stuartpittaway/diyBMSv4/ControllerCircuit/DIN_Rail_Case_Dimensions.jpeg

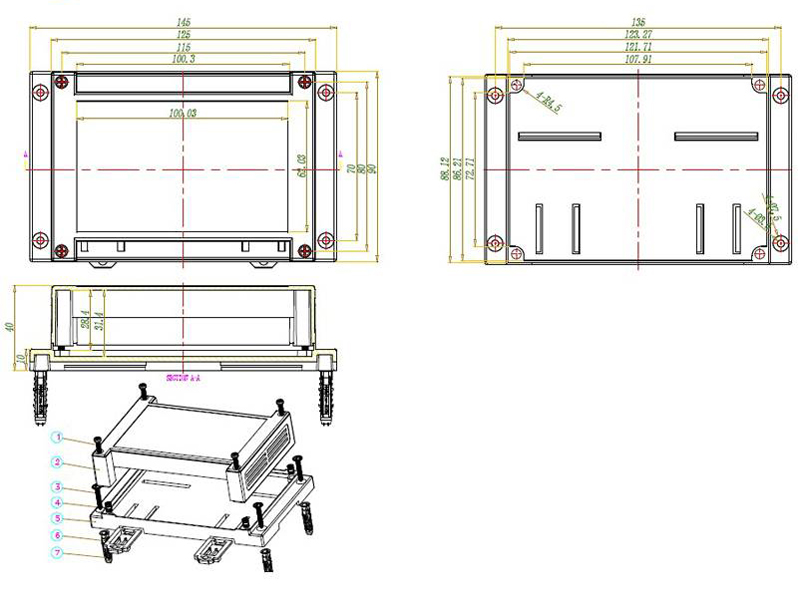
ControllerCircuit/DIN_Rail_Case_Dimensions.jpeg
