stuartpittaway/diyBMSv4/ControllerCircuit/ESP32boards.png

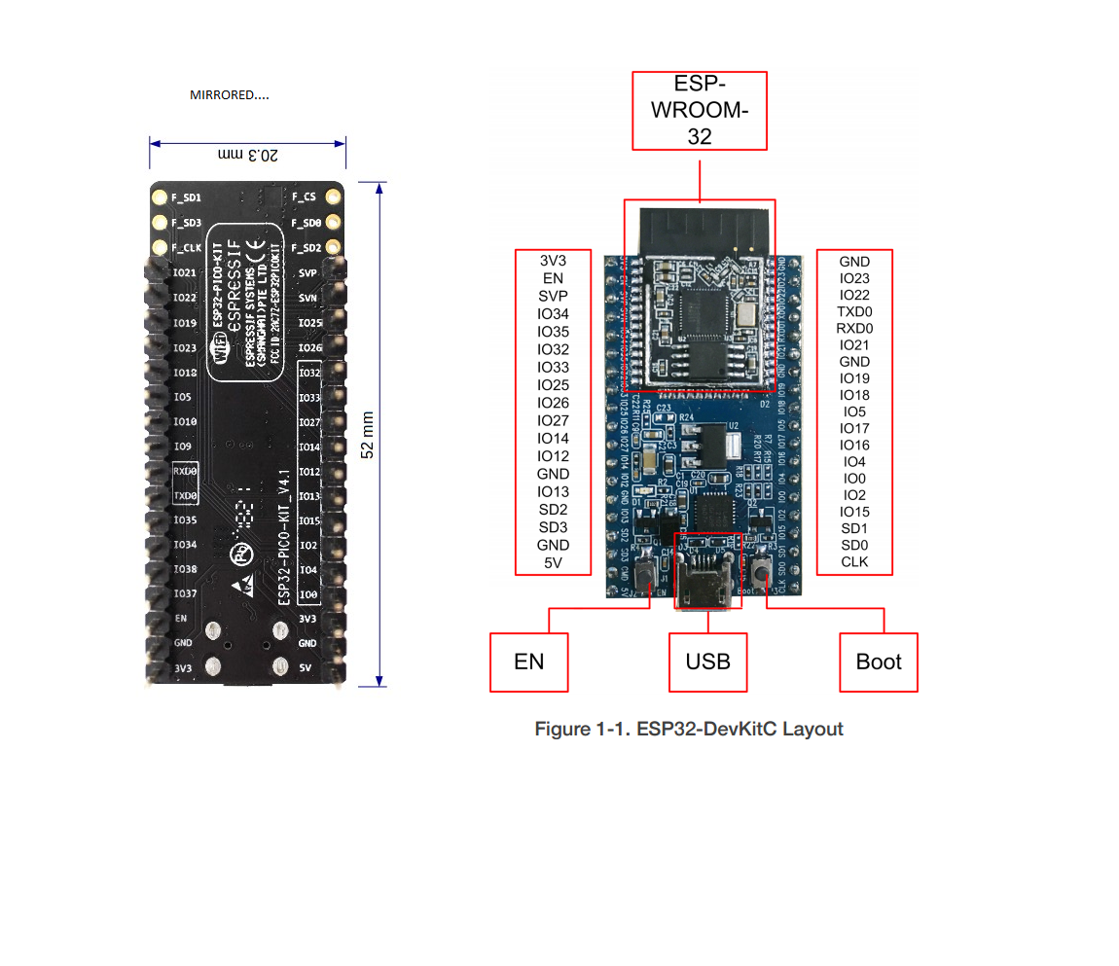
ControllerCircuit/ESP32boards.png
