stuartpittaway/diyBMSv4/ControllerCurrentShuntAddOn/export/ControllerCurrentShuntAddOn-bottom.png

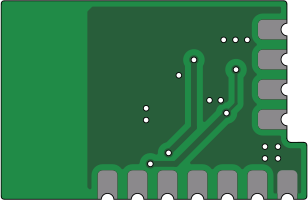
ControllerCurrentShuntAddOn/export/ControllerCurrentShuntAddOn-bottom.png
