stuartpittaway/diyBMSv4/ControllerCurrentShuntAddOn/export/ControllerCurrentShuntAddOn-top.png

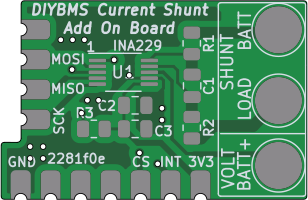
ControllerCurrentShuntAddOn/export/ControllerCurrentShuntAddOn-top.png
