stuartpittaway/diyBMSv4/ModuleV450/export/ModuleV450-bottom.png

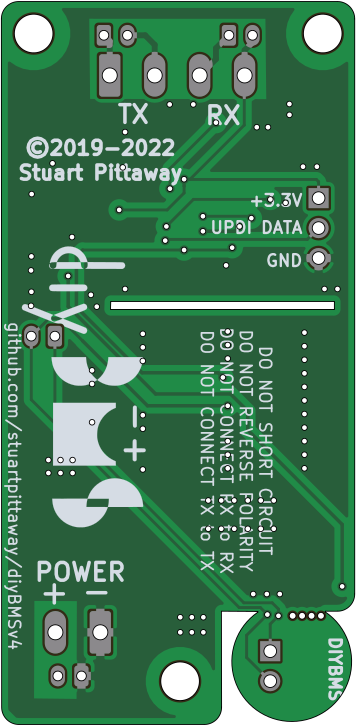
ModuleV450/export/ModuleV450-bottom.png
