stuartpittaway/diyBMSv4/ModuleV490-AllInOne/export/Module_16S-bottom.png

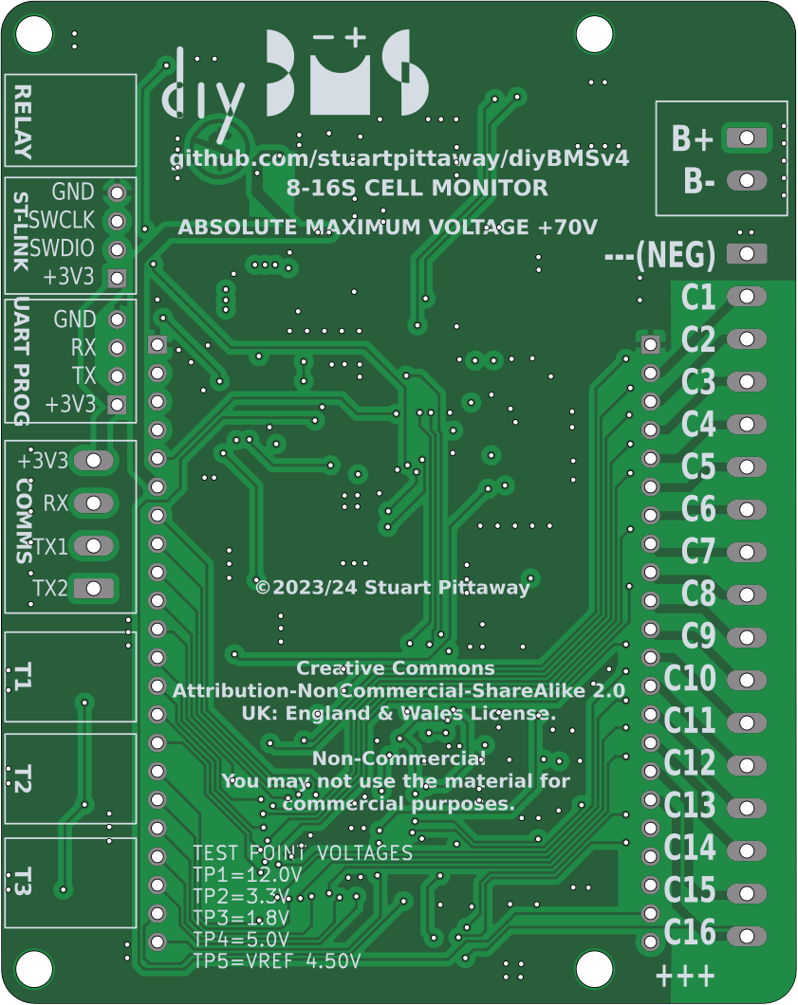
ModuleV490-AllInOne/export/Module_16S-bottom.png
