stuartpittaway/diyBMSv4/ModuleV490-AllInOne/export/Module_16S-top.png

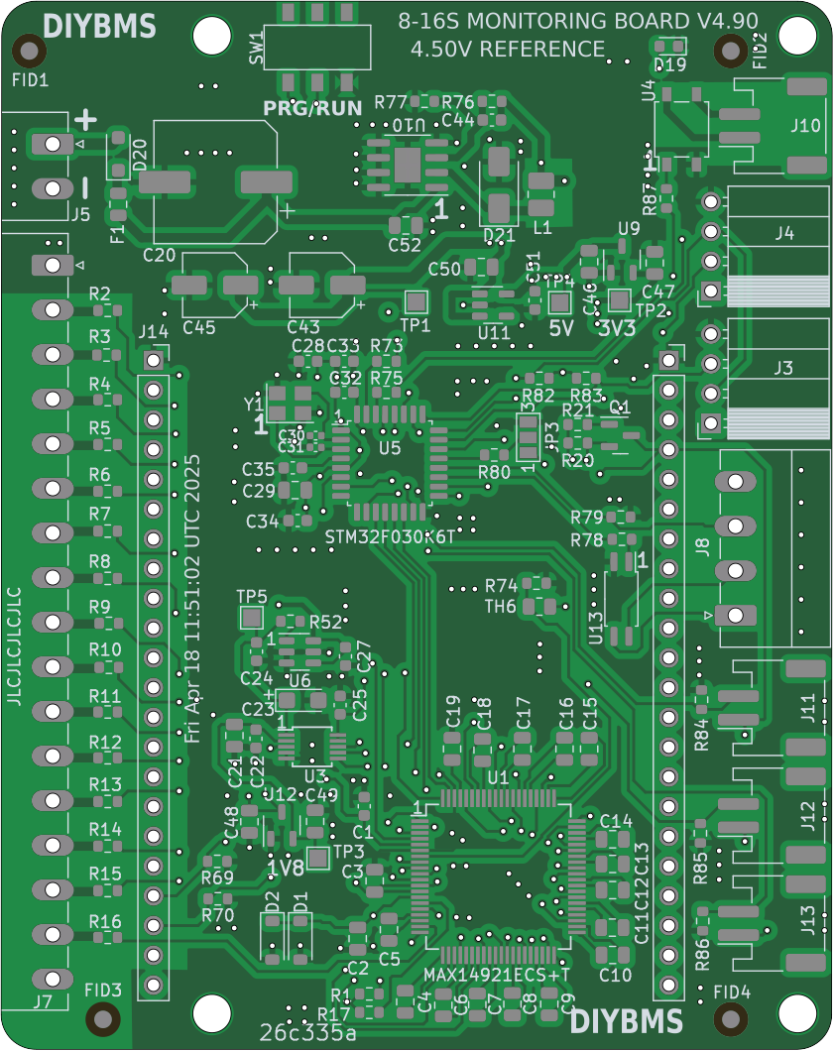
ModuleV490-AllInOne/export/Module_16S-top.png
