stuartpittaway/diyBMSv4/ModuleV490-PassiveBal/export/Module_16S_PassiveBalanceAddOn-bottom.png

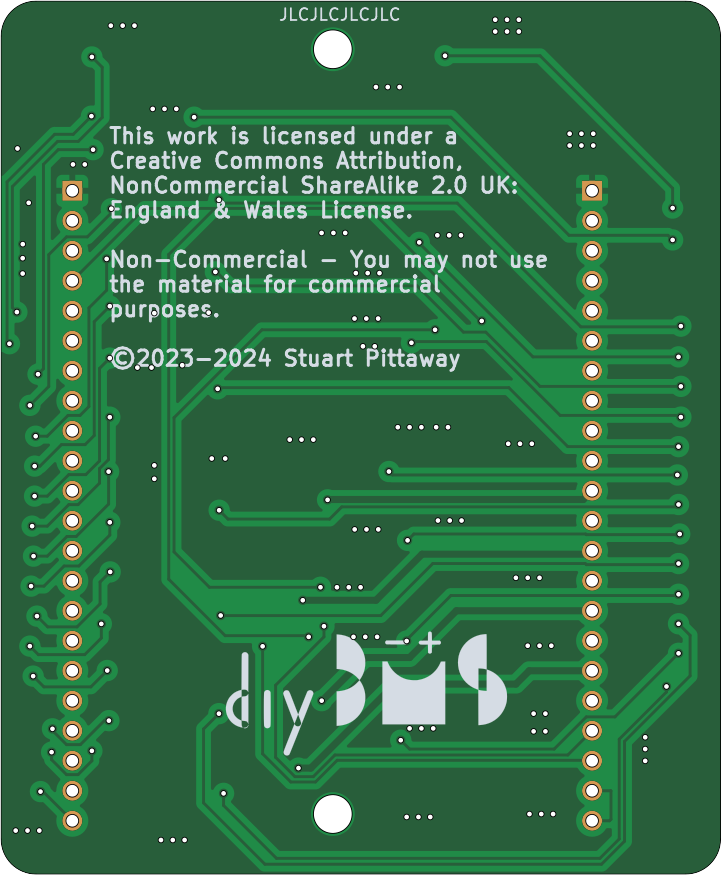
ModuleV490-PassiveBal/export/Module_16S_PassiveBalanceAddOn-bottom.png
