stuartpittaway/diyBMSv4/TemperaturePCB/export/TemperaturePCB-bottom.png

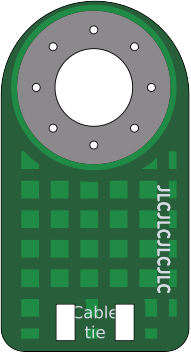
TemperaturePCB/export/TemperaturePCB-bottom.png
