stuartpittaway/diyBMSv4/ModuleV490-AllInOne/export/PCB.pdf

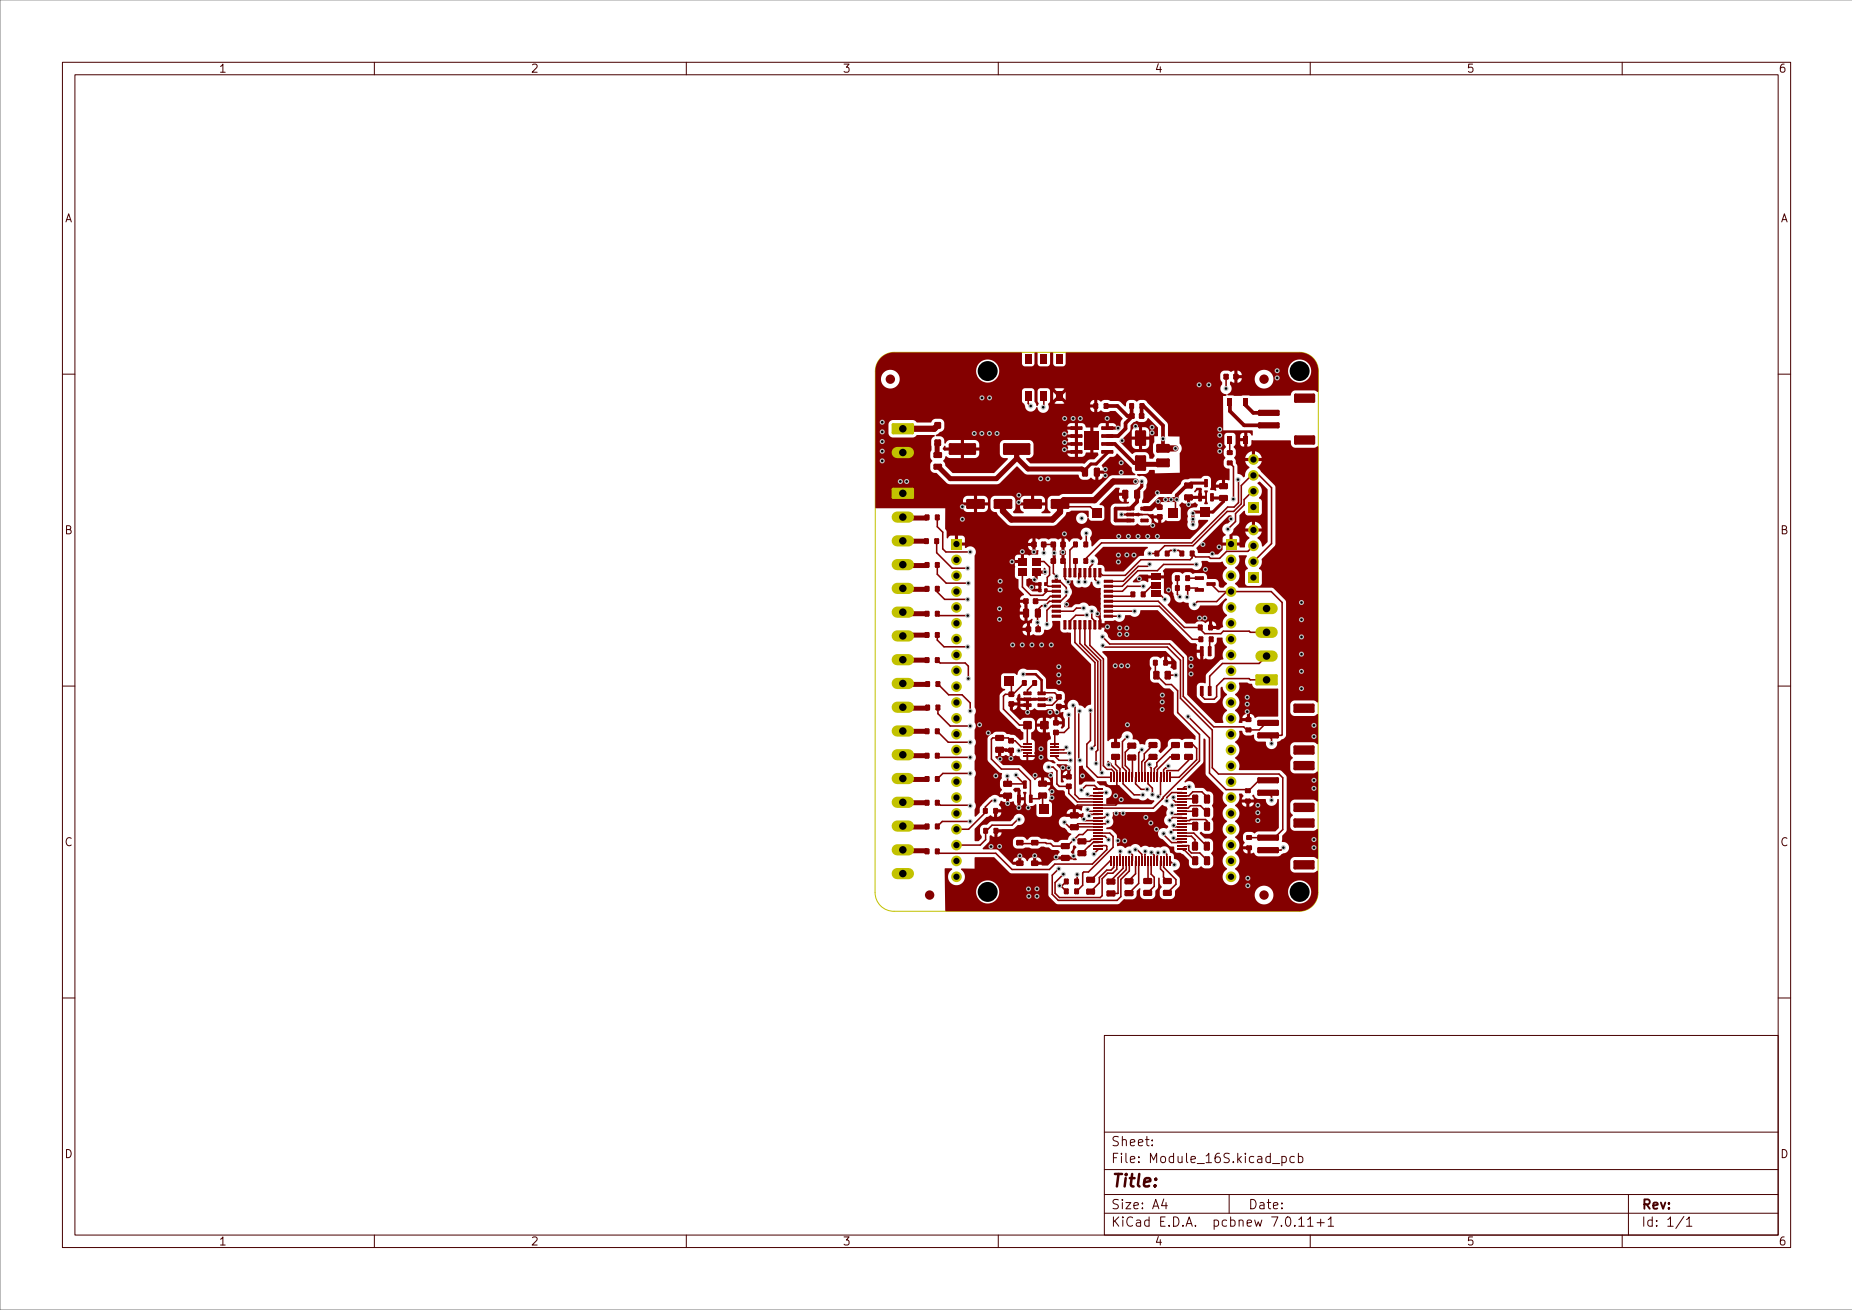
[picture p57: page 1]

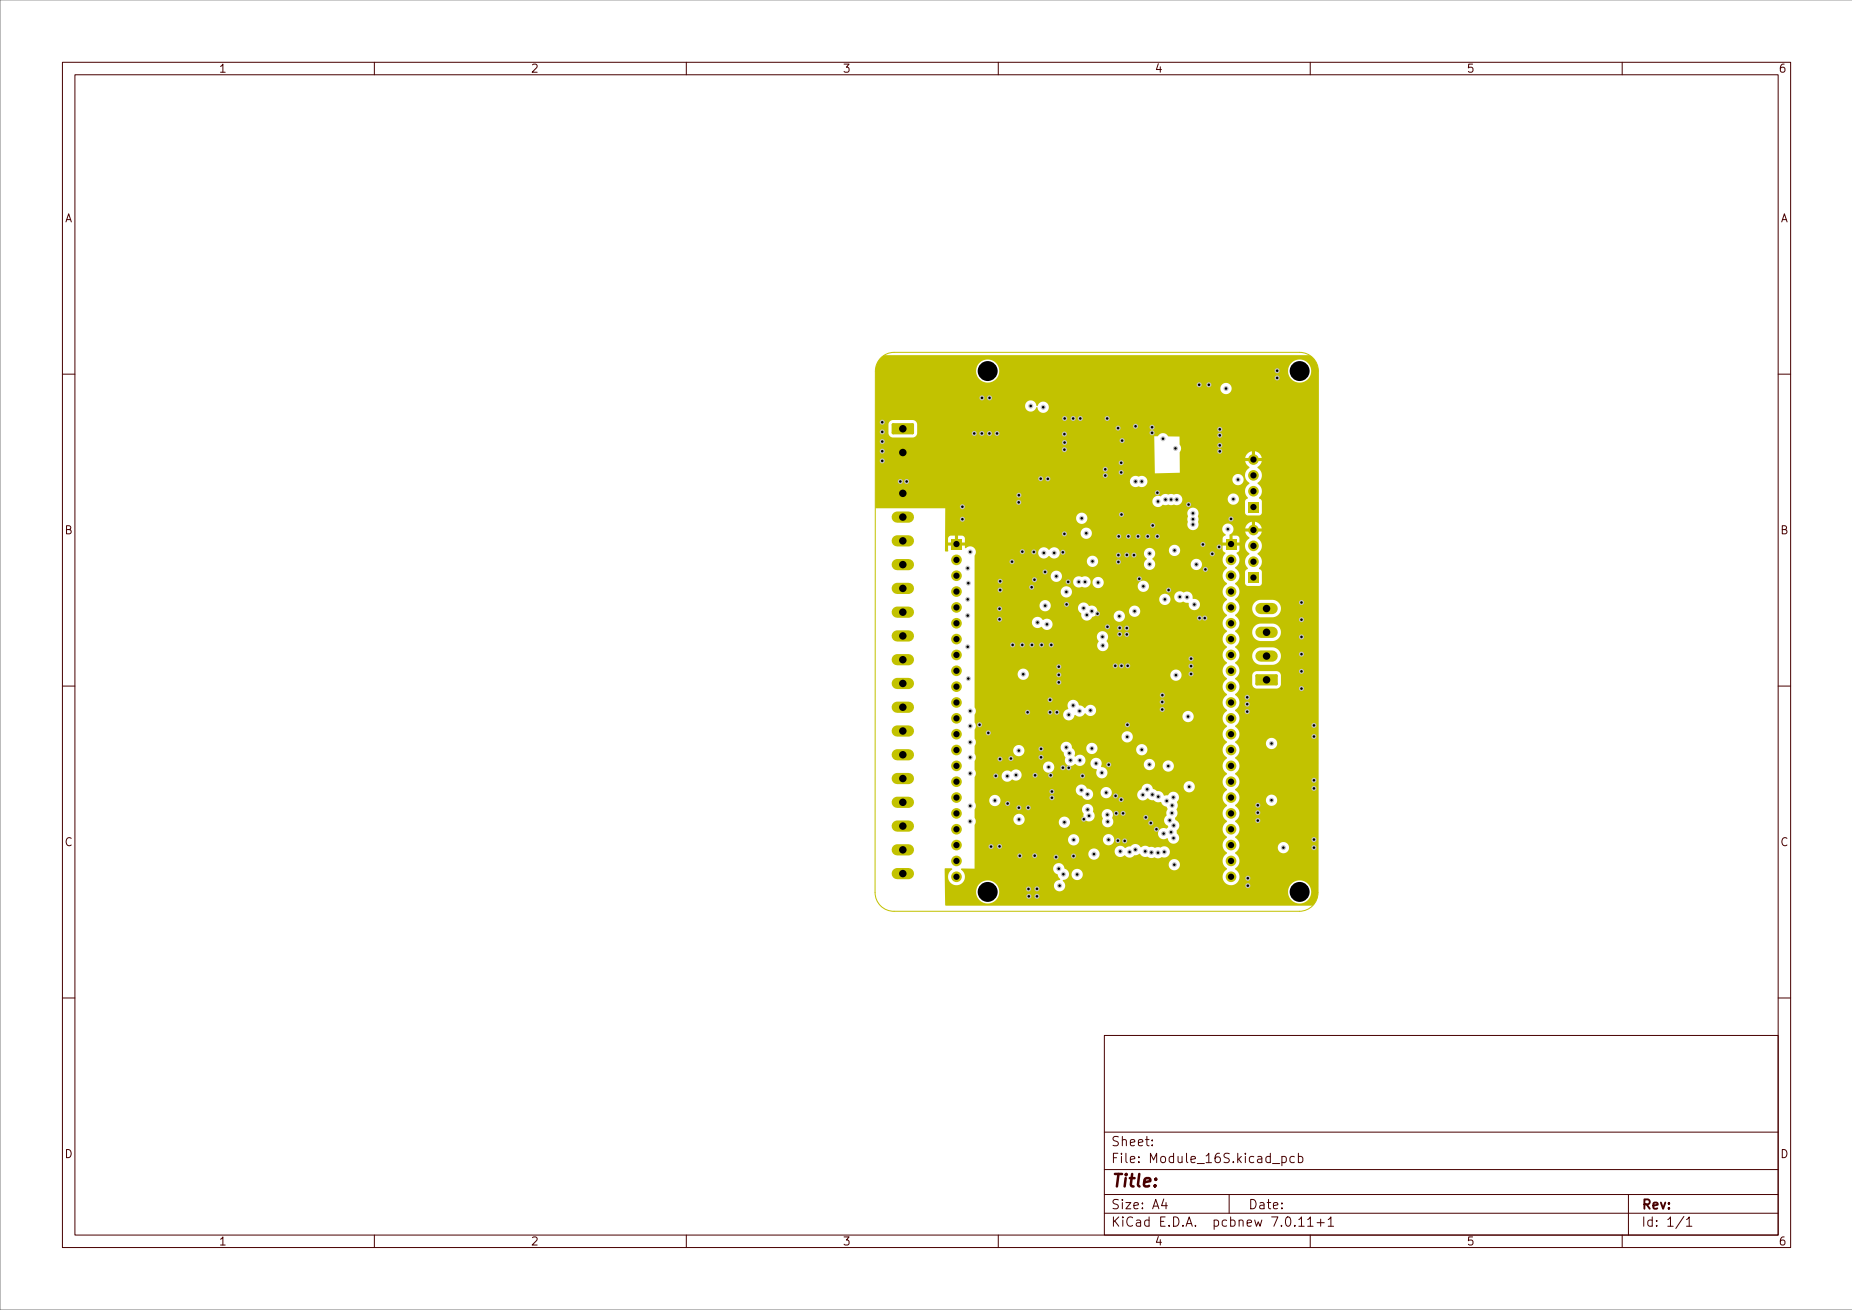
[picture p58: page 2]

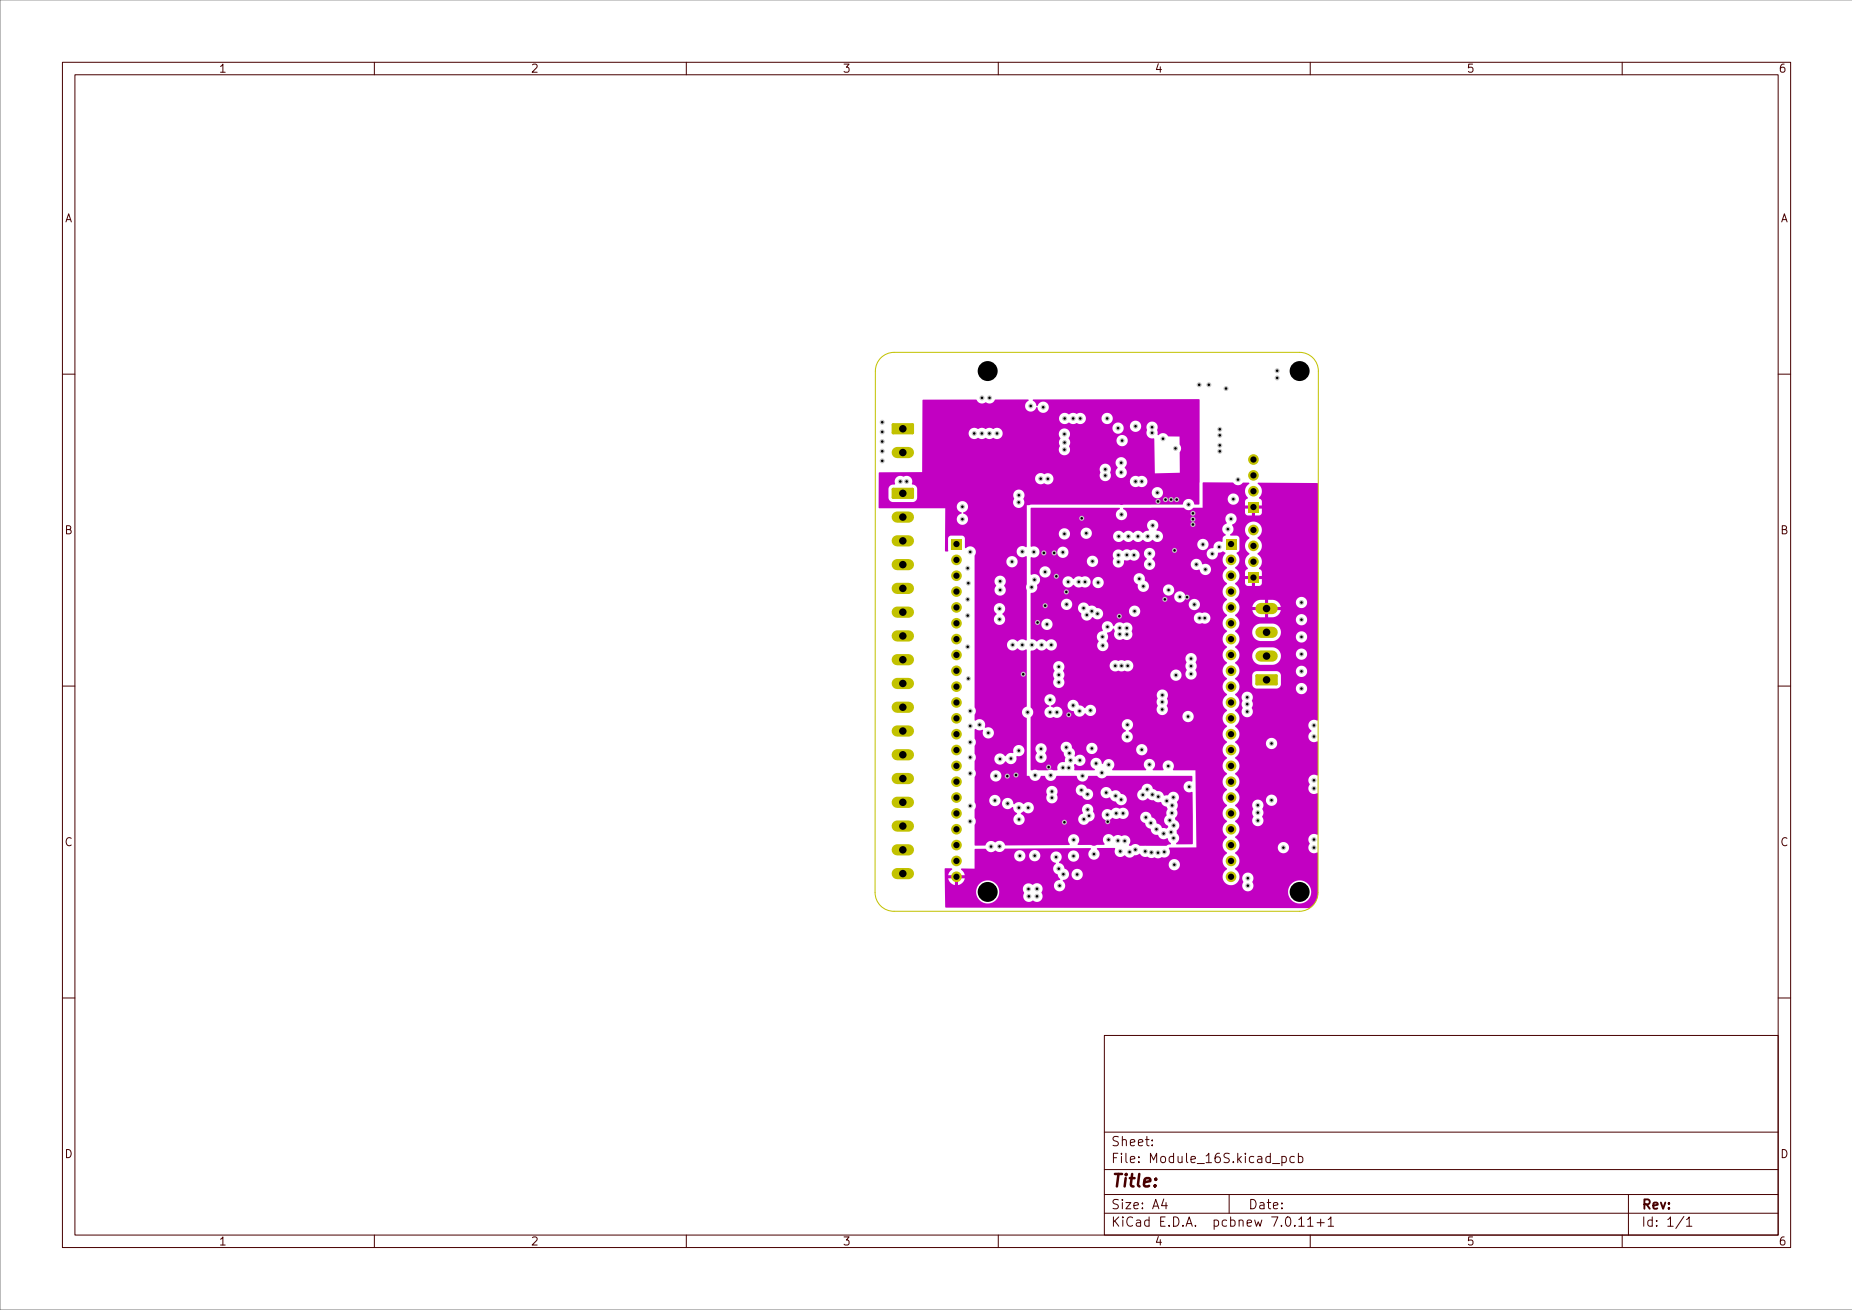
[picture p59: page 3]

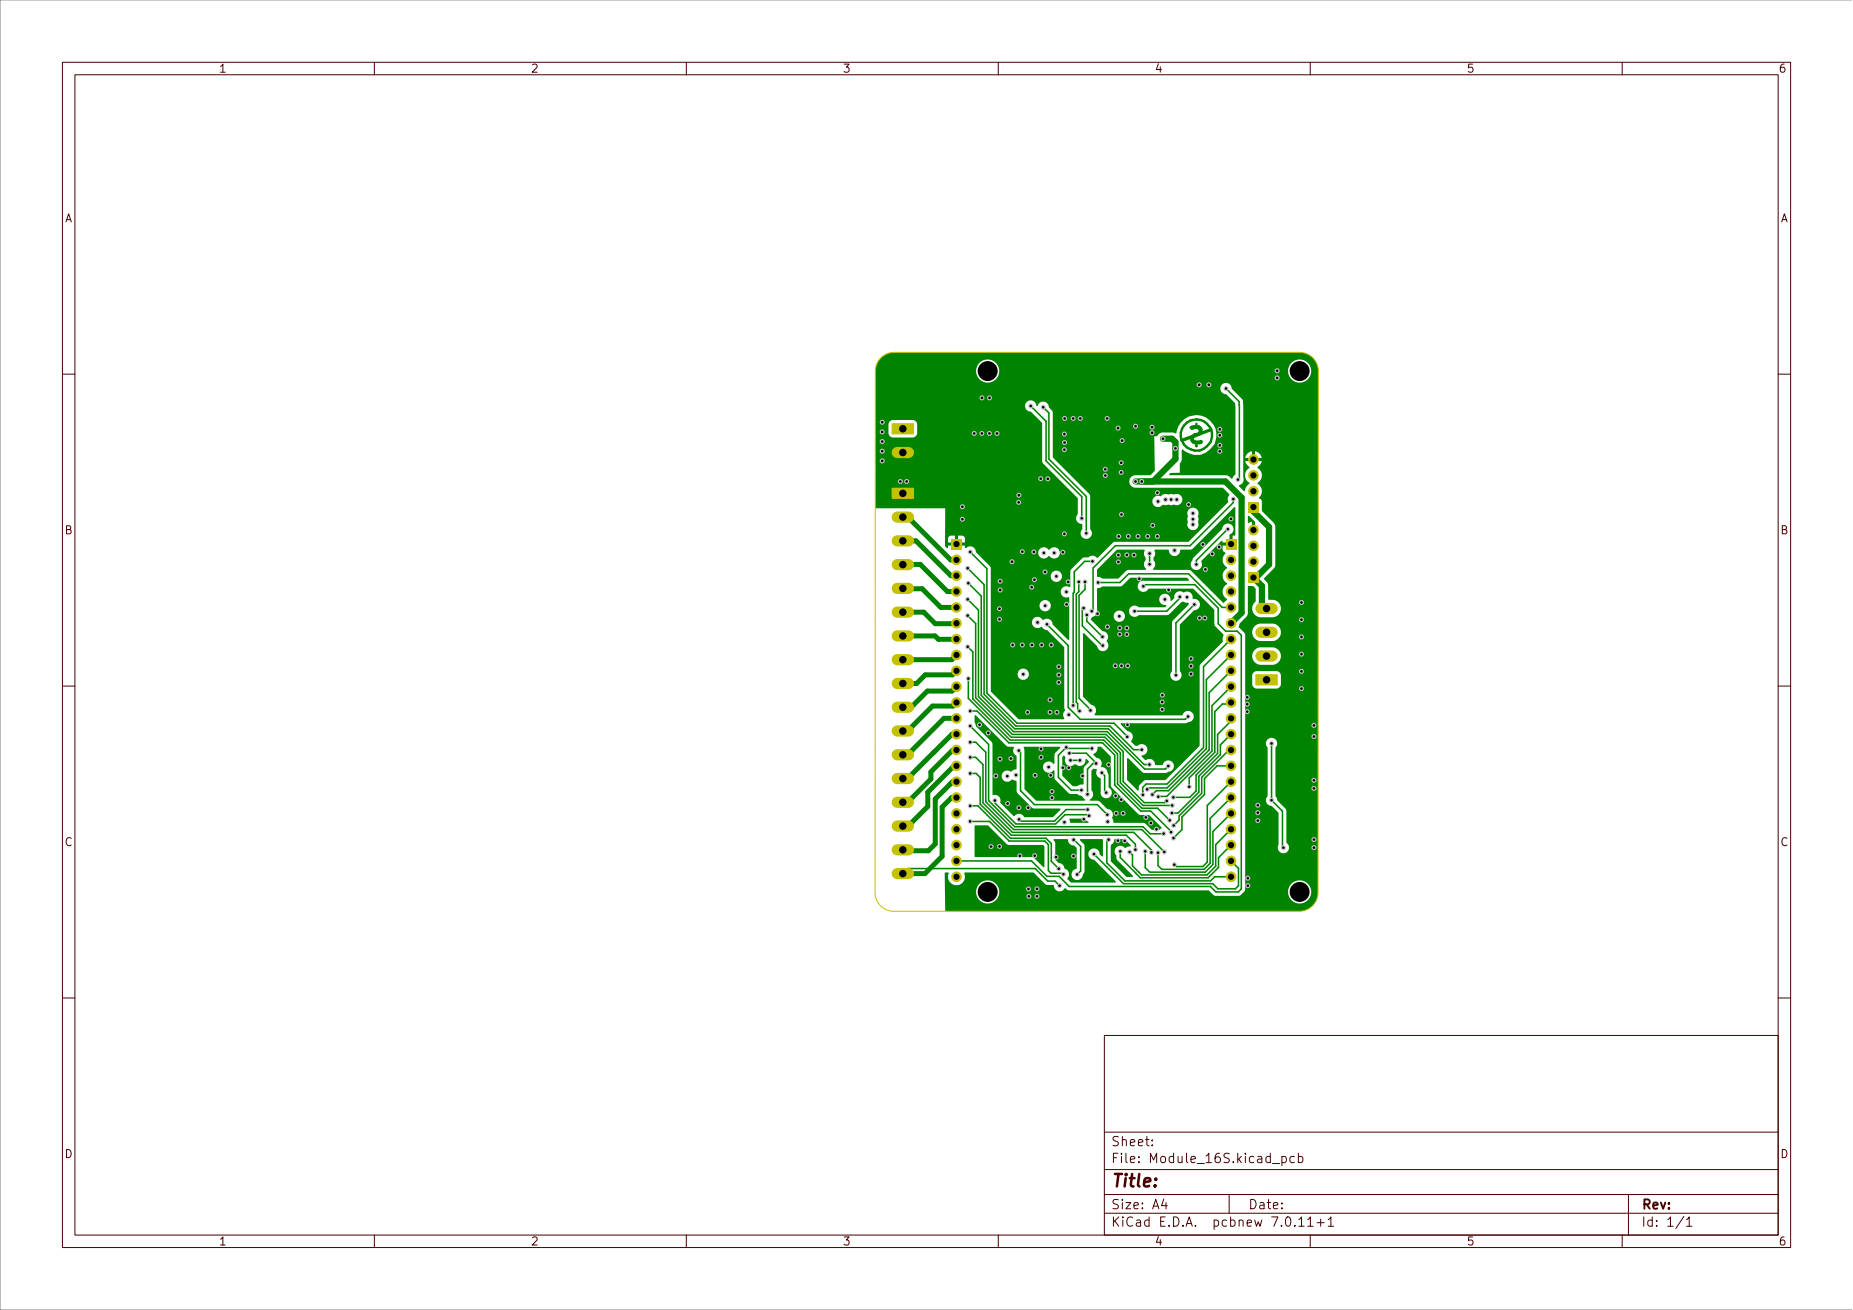
[picture p60: page 4]

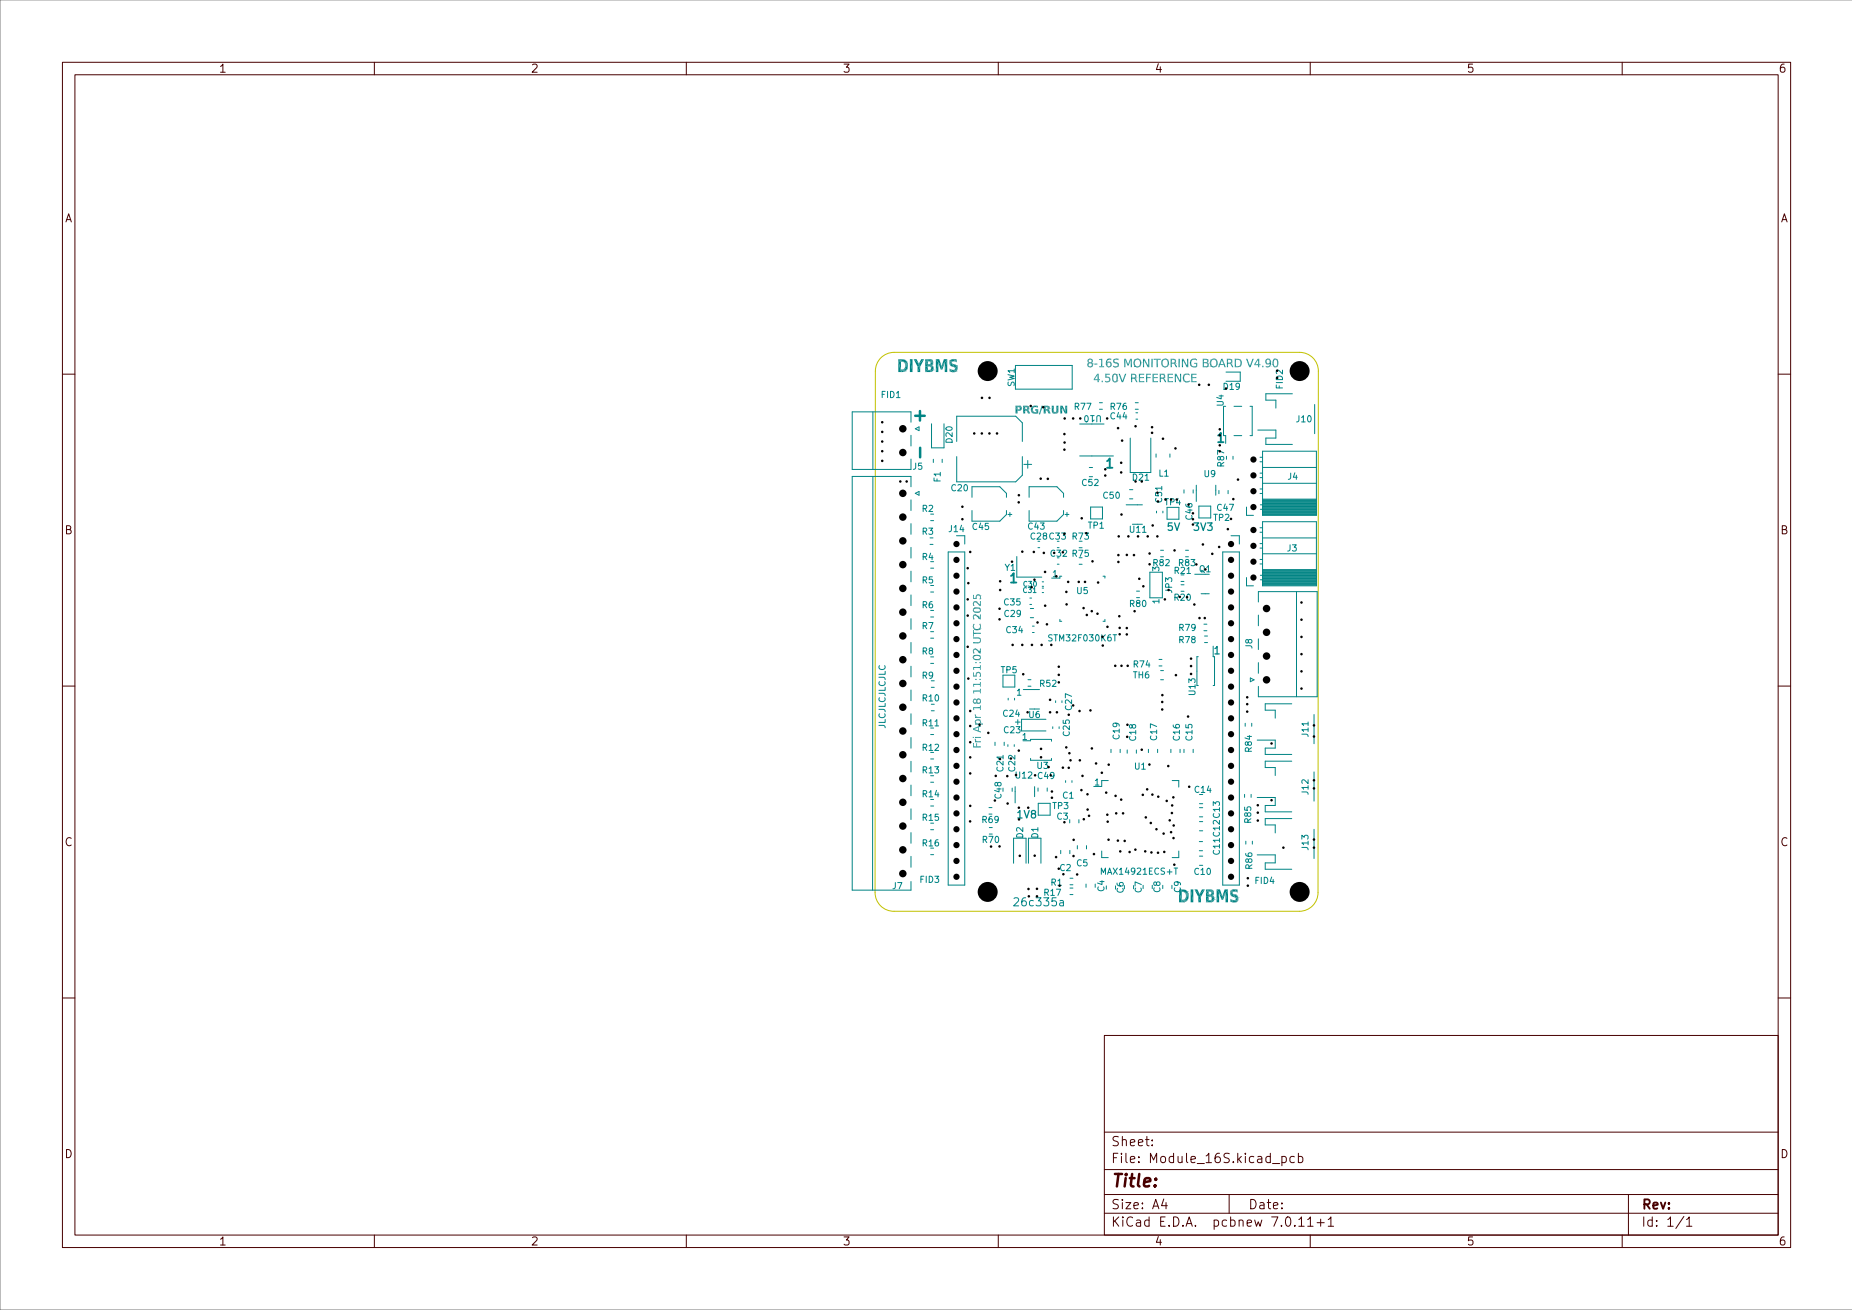
[picture p61: page 5]

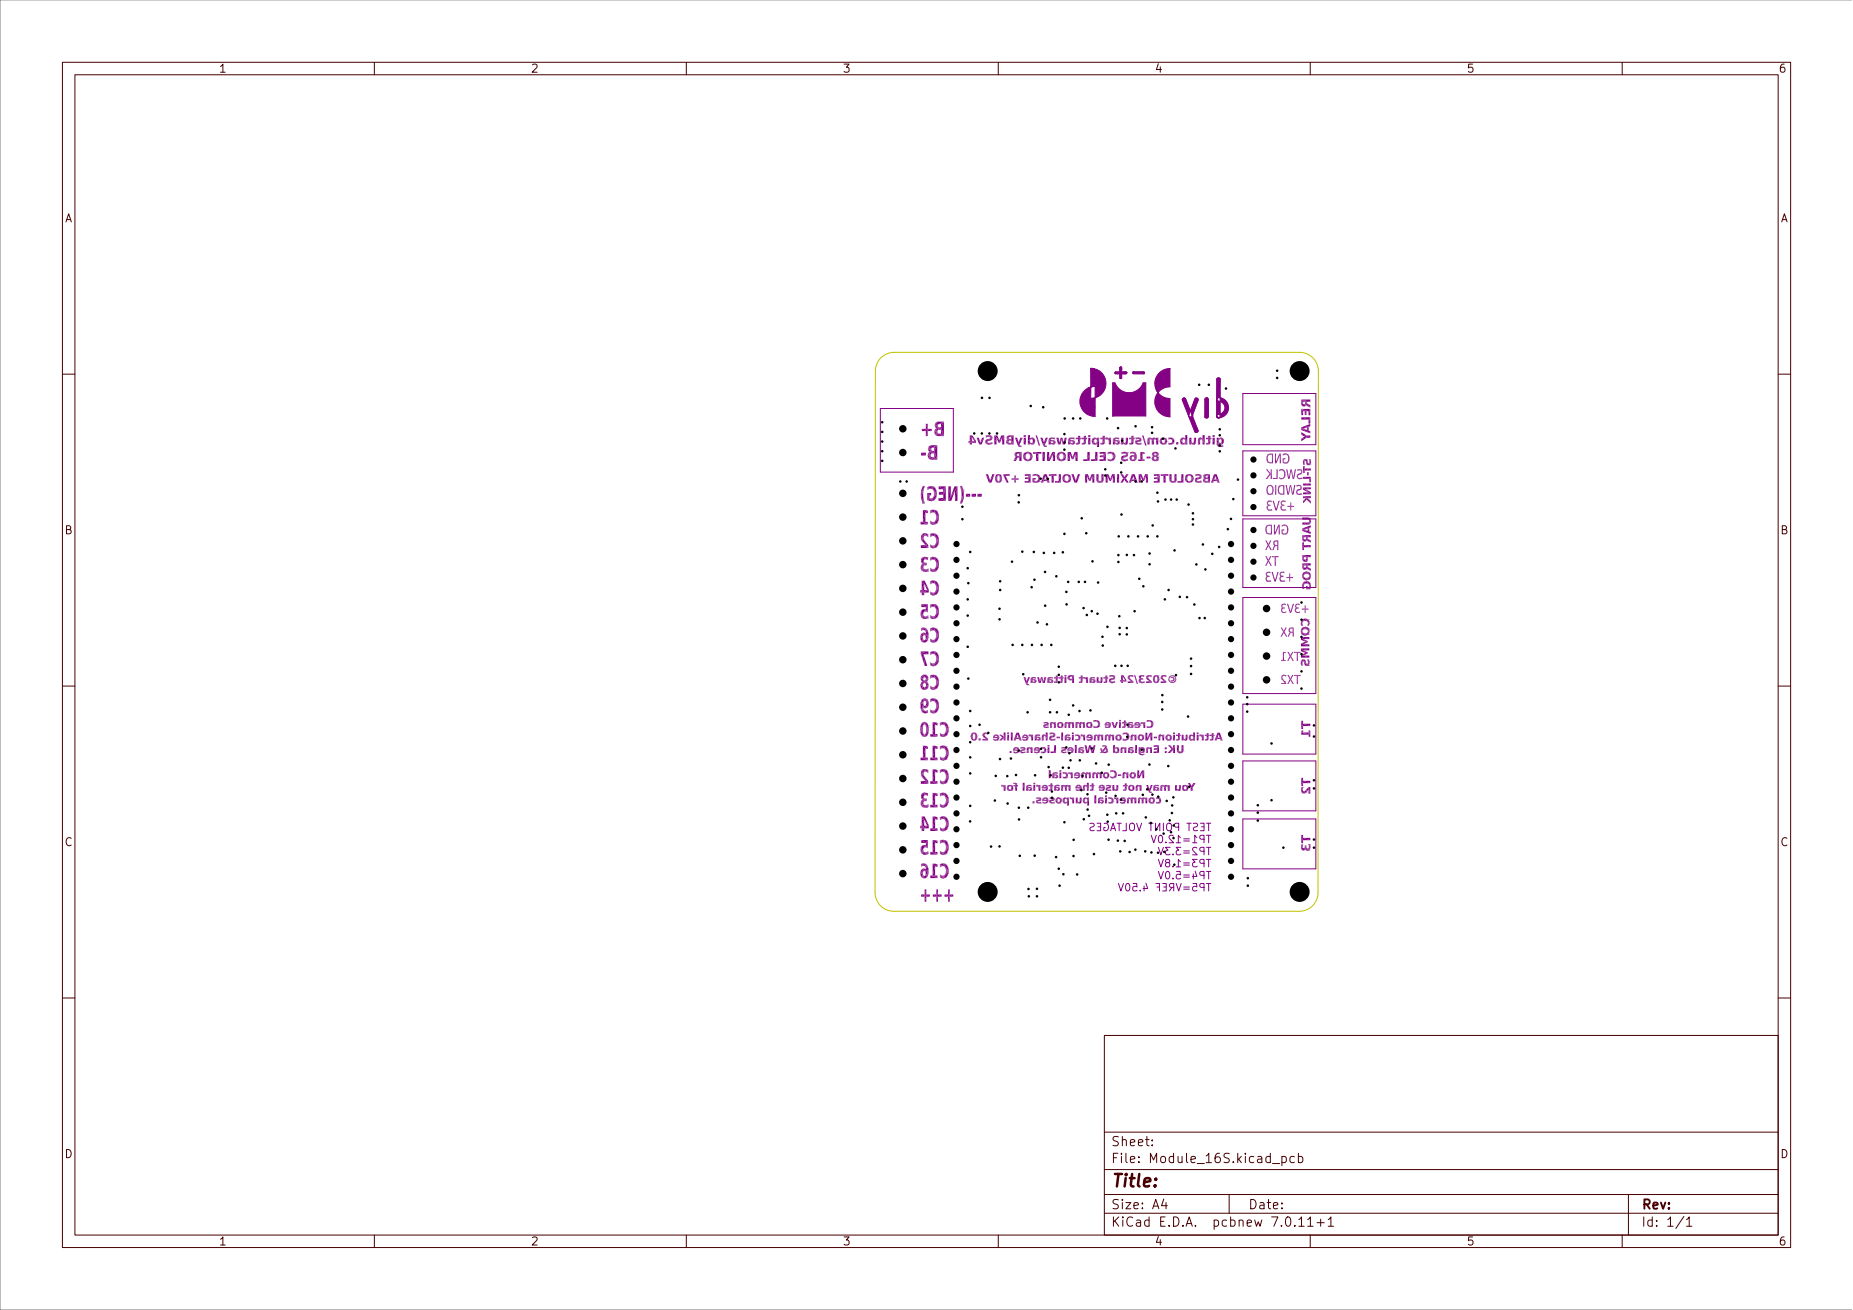
[picture p62: page 6]
