stuartpittaway/diyBMSv4/ModuleV440/export/Schematic.pdf

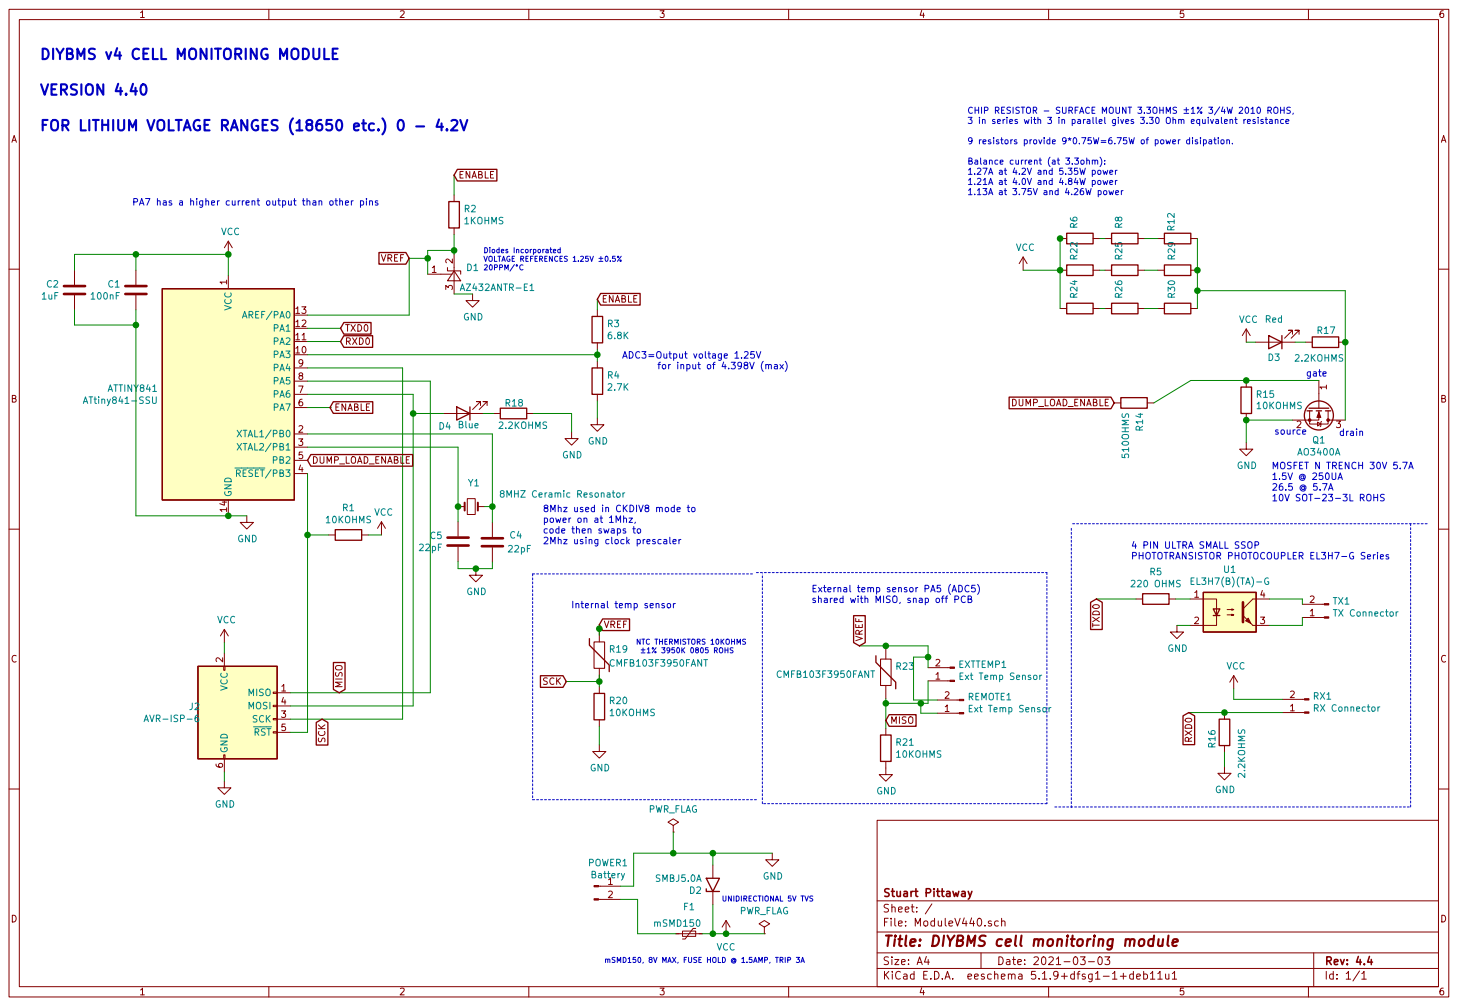
[picture p63: page 1]

source DIYBMS v4 CELL MONITORING MODULE

FOR LITHIUM VOLTAGE RANGES (18650 etc.) 0 - 4.2V

9 resistors provide 9*0.75W=6.75W of power disipation. Balance current (at 3.3ohm): 1.27A at 4.2V and 5.35W power 1.21A at 4.0V and 4.84W power 1.13A at 3.75V and 4.26W power

PA7 has a higher current output than other pins

1 PA3 10 PA2 11 PA1 12 AREF/PA0 13 GND 14 XTAL1/PB0 2 XTAL2/PB1 3 RESET/PB3 4 PB2 5 PA7 6 PA6 7 PA5 8 PA4 9 ATTINY841 ATtiny841-SSU GND

8Mhz used in CKDIV8 mode to power on at 1Mhz,

code then swaps to

4 PIN ULTRA SMALL SSOP
PHOTOTRANSISTOR PHOTOCOUPLER EL3H7-G Series
220 OHMS

shared with MISO, snap off PCB

2 SCK 3 MOSI 4 RST 5 GND

File: ModuleV440.sch Sheet: / Stuart Pittaway

Id: 1/1 Title: DIYBMS cell monitoring module

mSMD150, 8V MAX, FUSE HOLD @ 1.5AMP, TRIP 3A
