stuartpittaway/diyBMSv4/ModuleV421/circuit.pdf

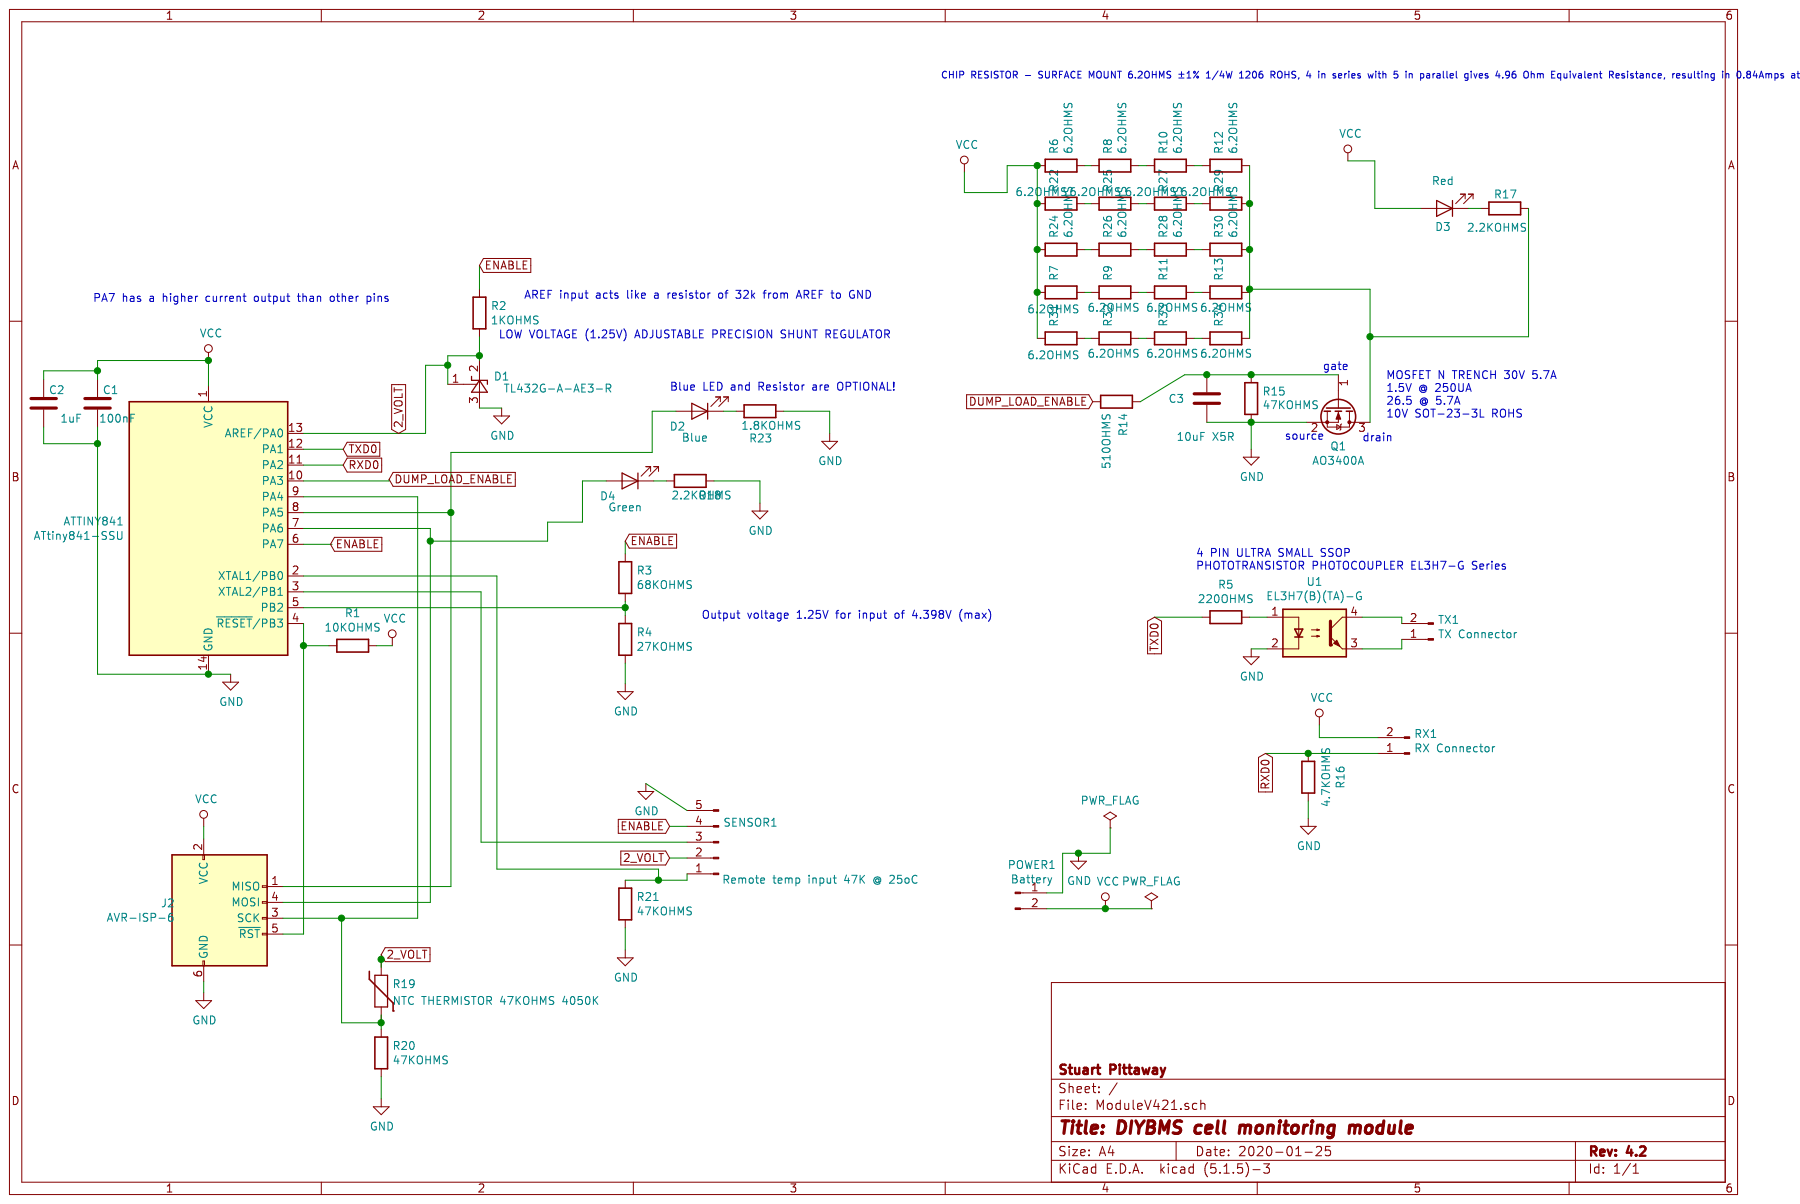
[picture p64: page 1]
