stuartpittaway/diyBMSv4/ModuleV400/pcb.pdf

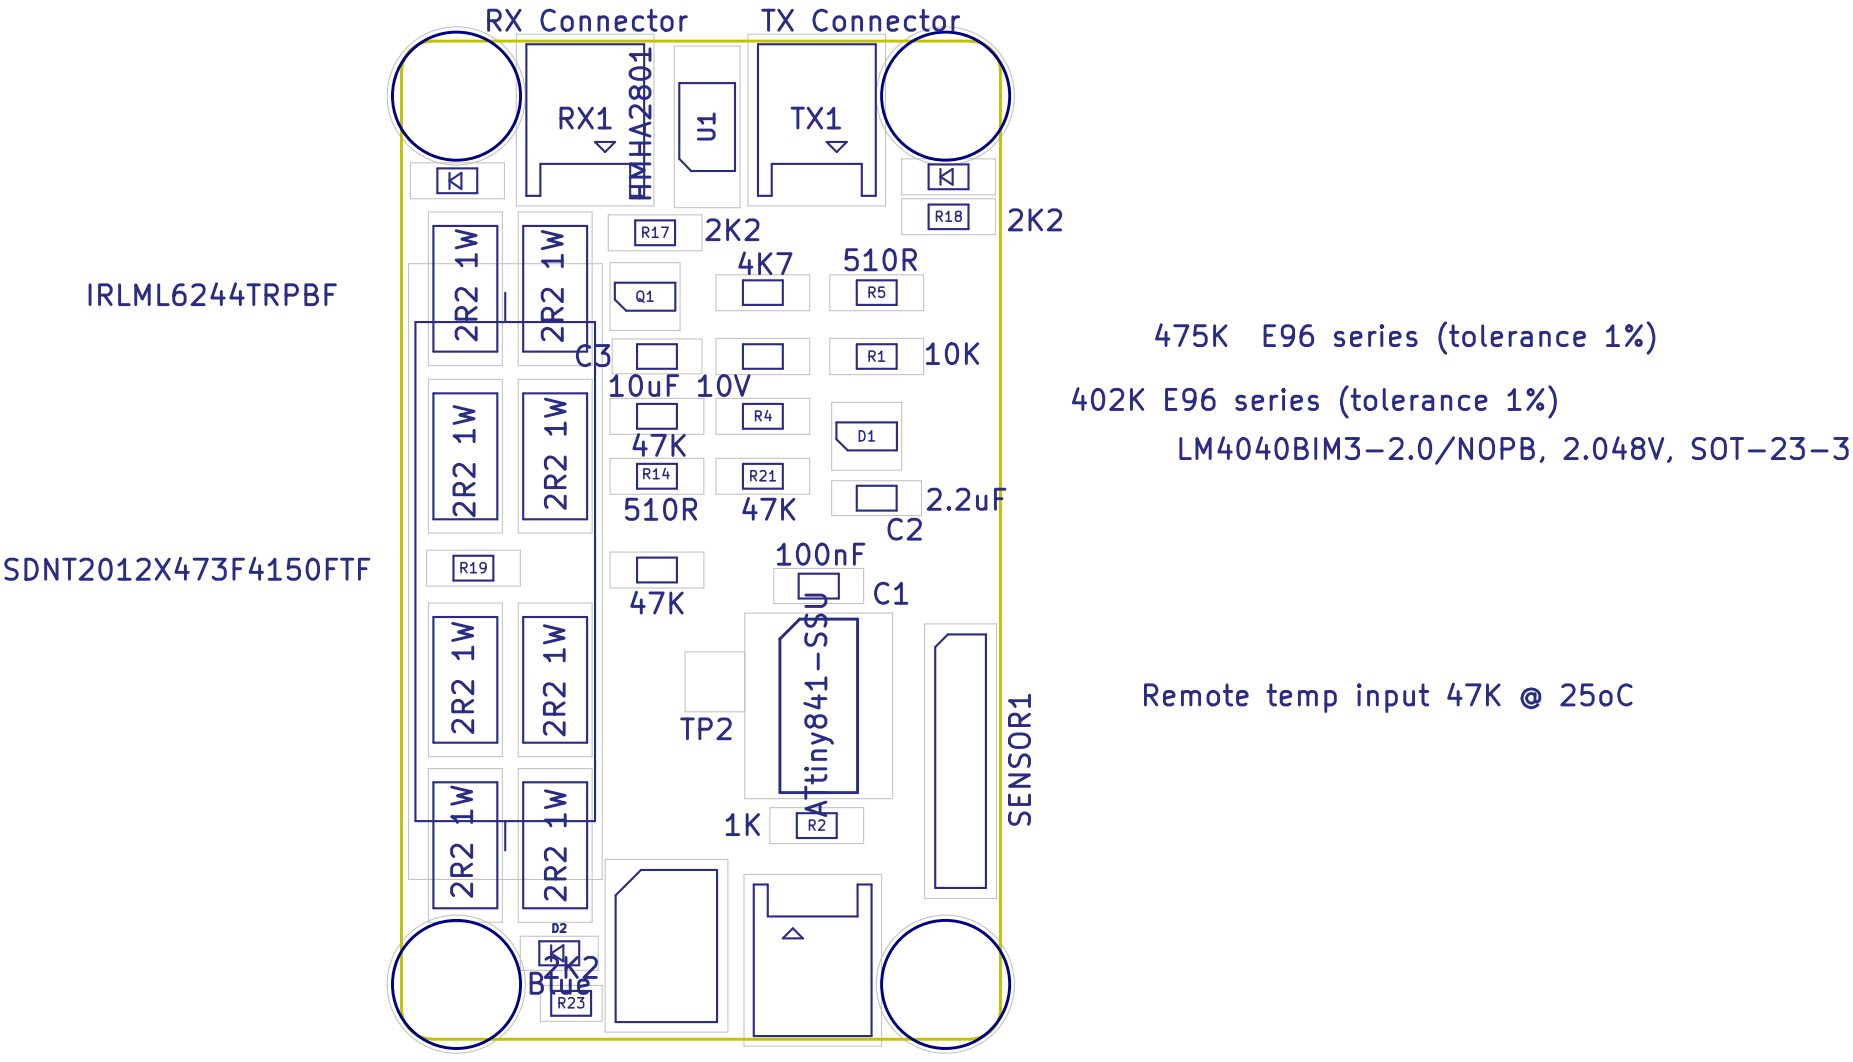
[picture p65: page 1]
