stuartpittaway/diyBMSv4/ModuleV400/circuit.pdf

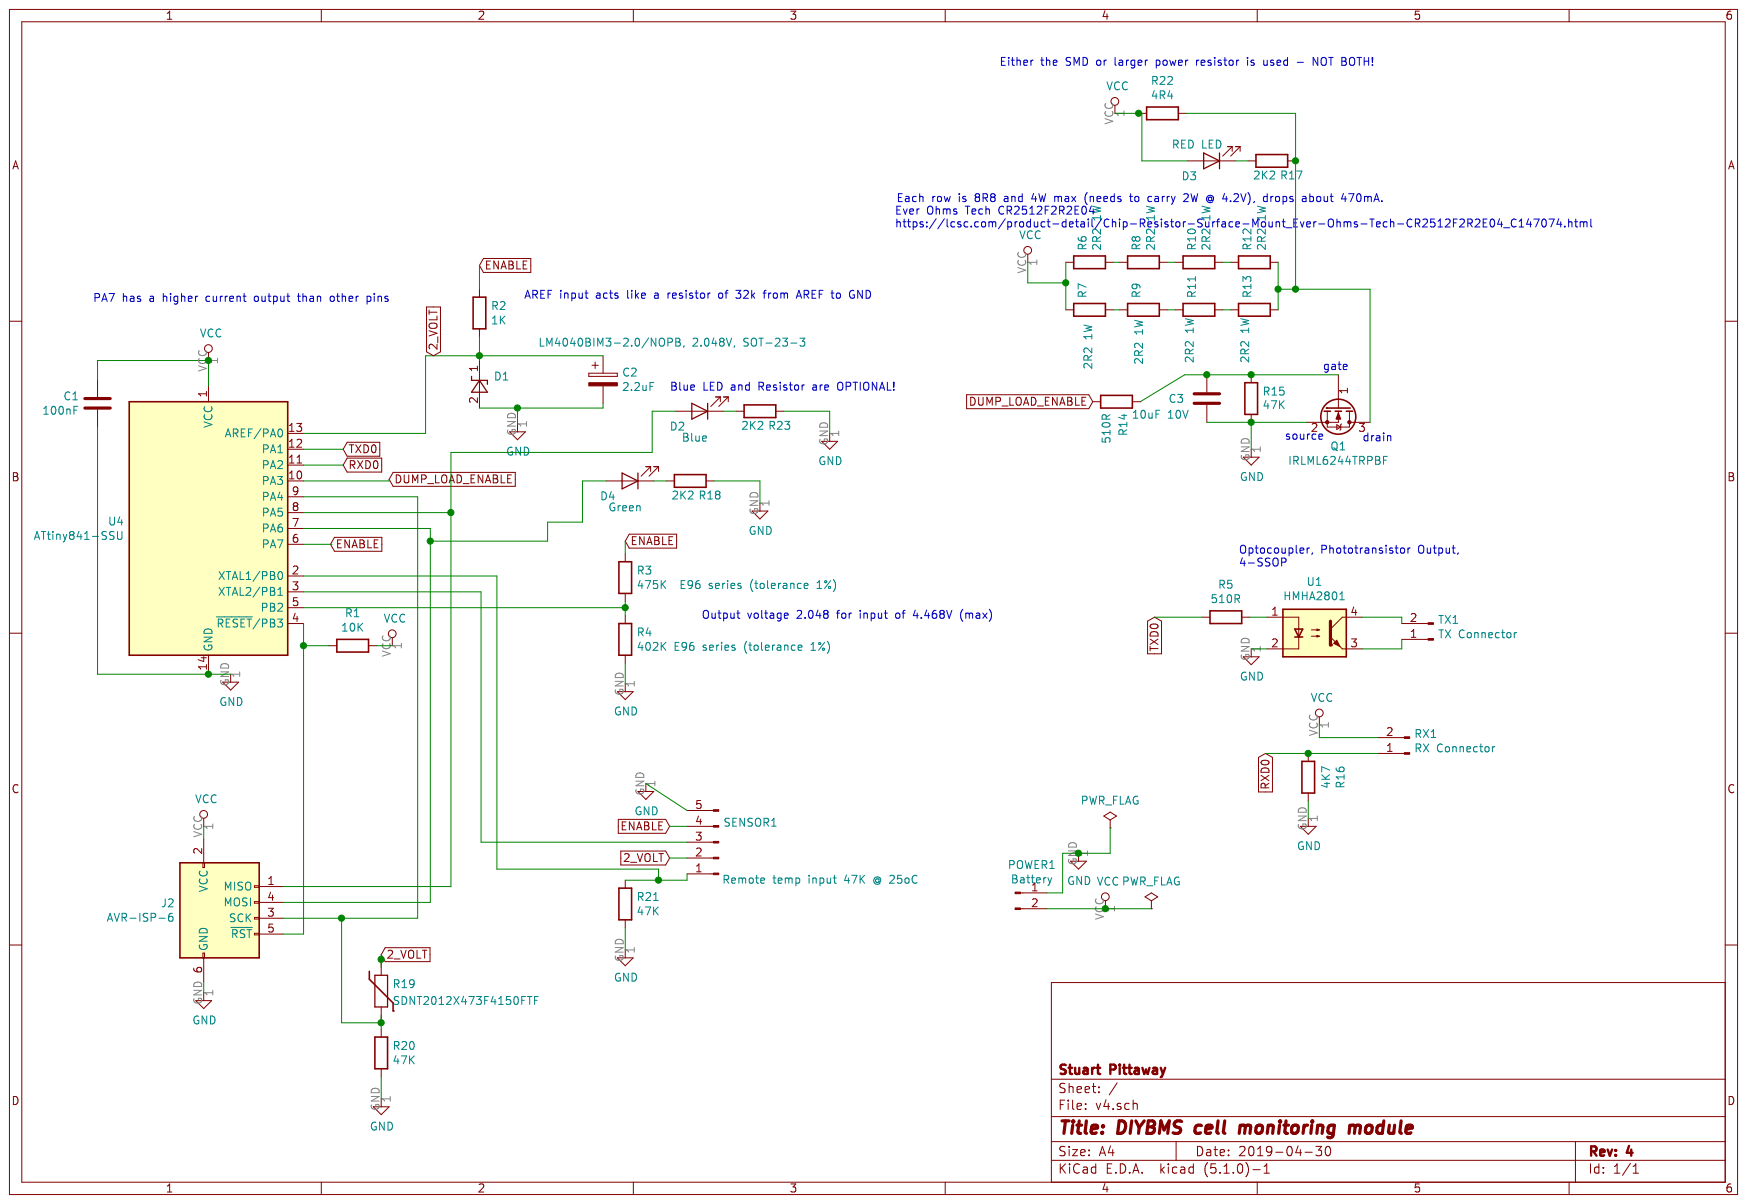
[picture p66: page 1]
