stuartpittaway/diyBMSv4/ModuleV440/export/PCB.pdf

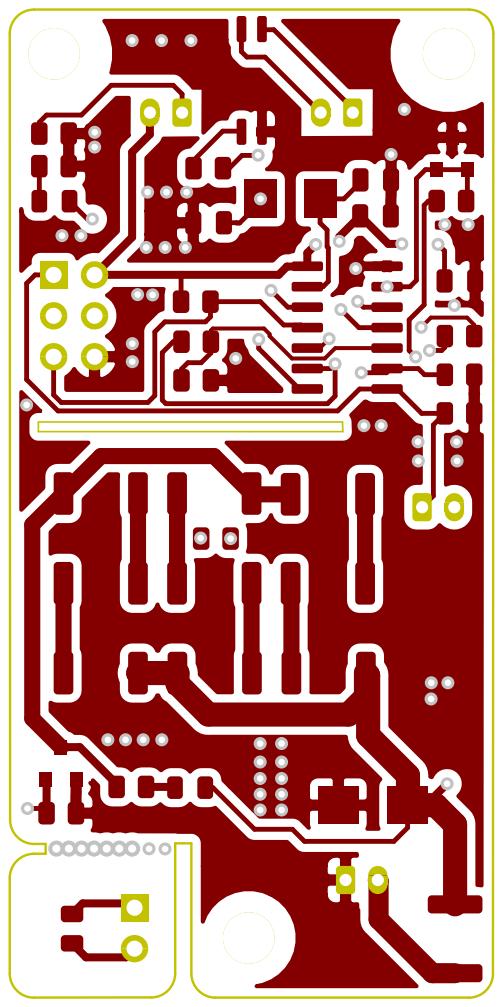
[picture p67: page 1]

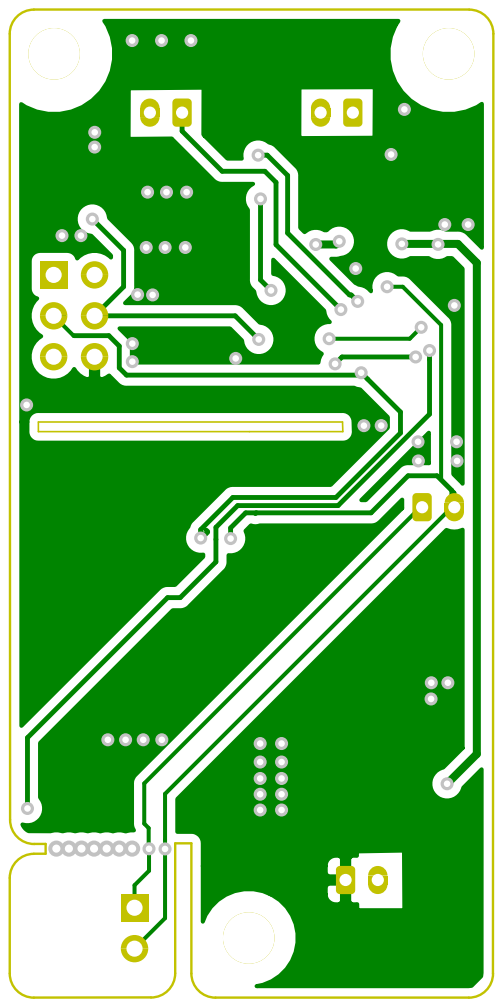
[picture p68: page 2]

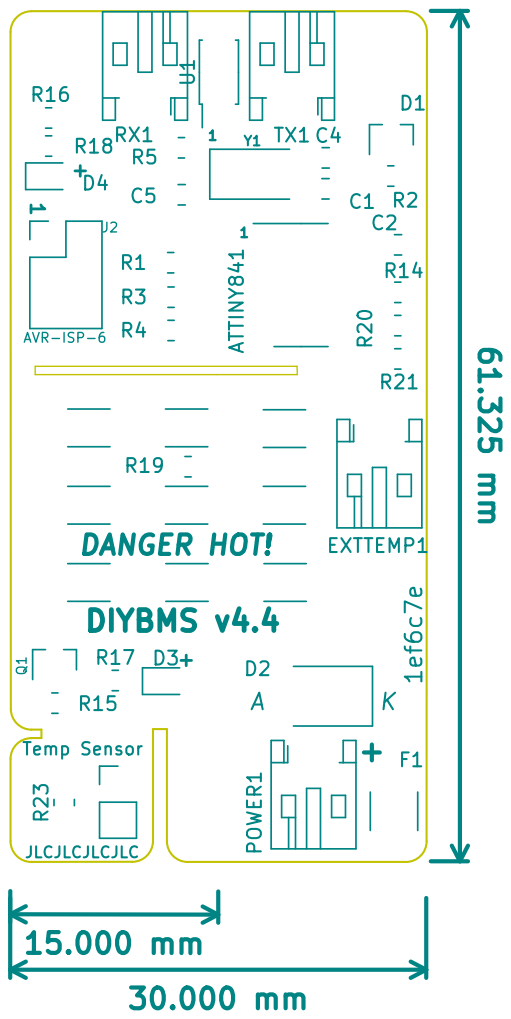
[picture p69: page 3]

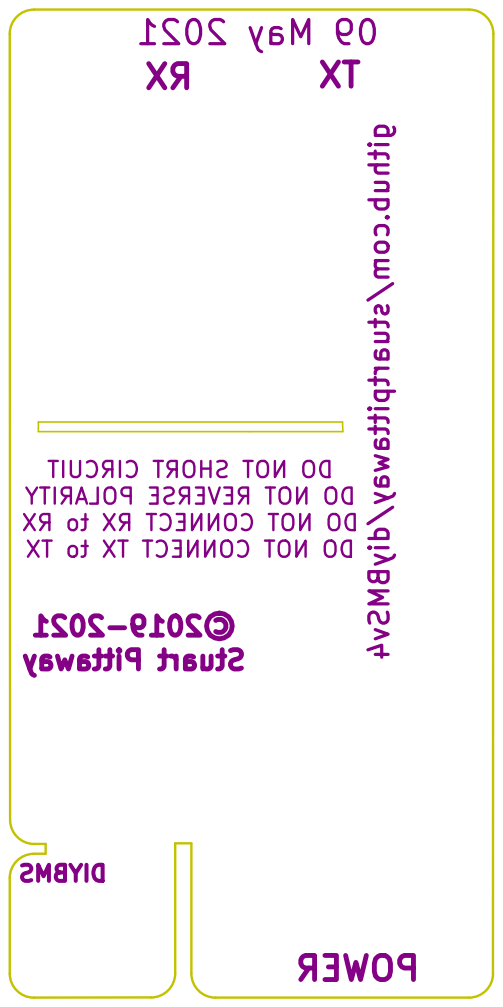
[picture p70: page 4]
